requireiot/MySoilSensorESP32/hardware/MySoilSensorESP32.kicad_sch

## KiCad design hardware/MySoilSensorESP32.kicad_sch (2024-08-03, an earlier design)

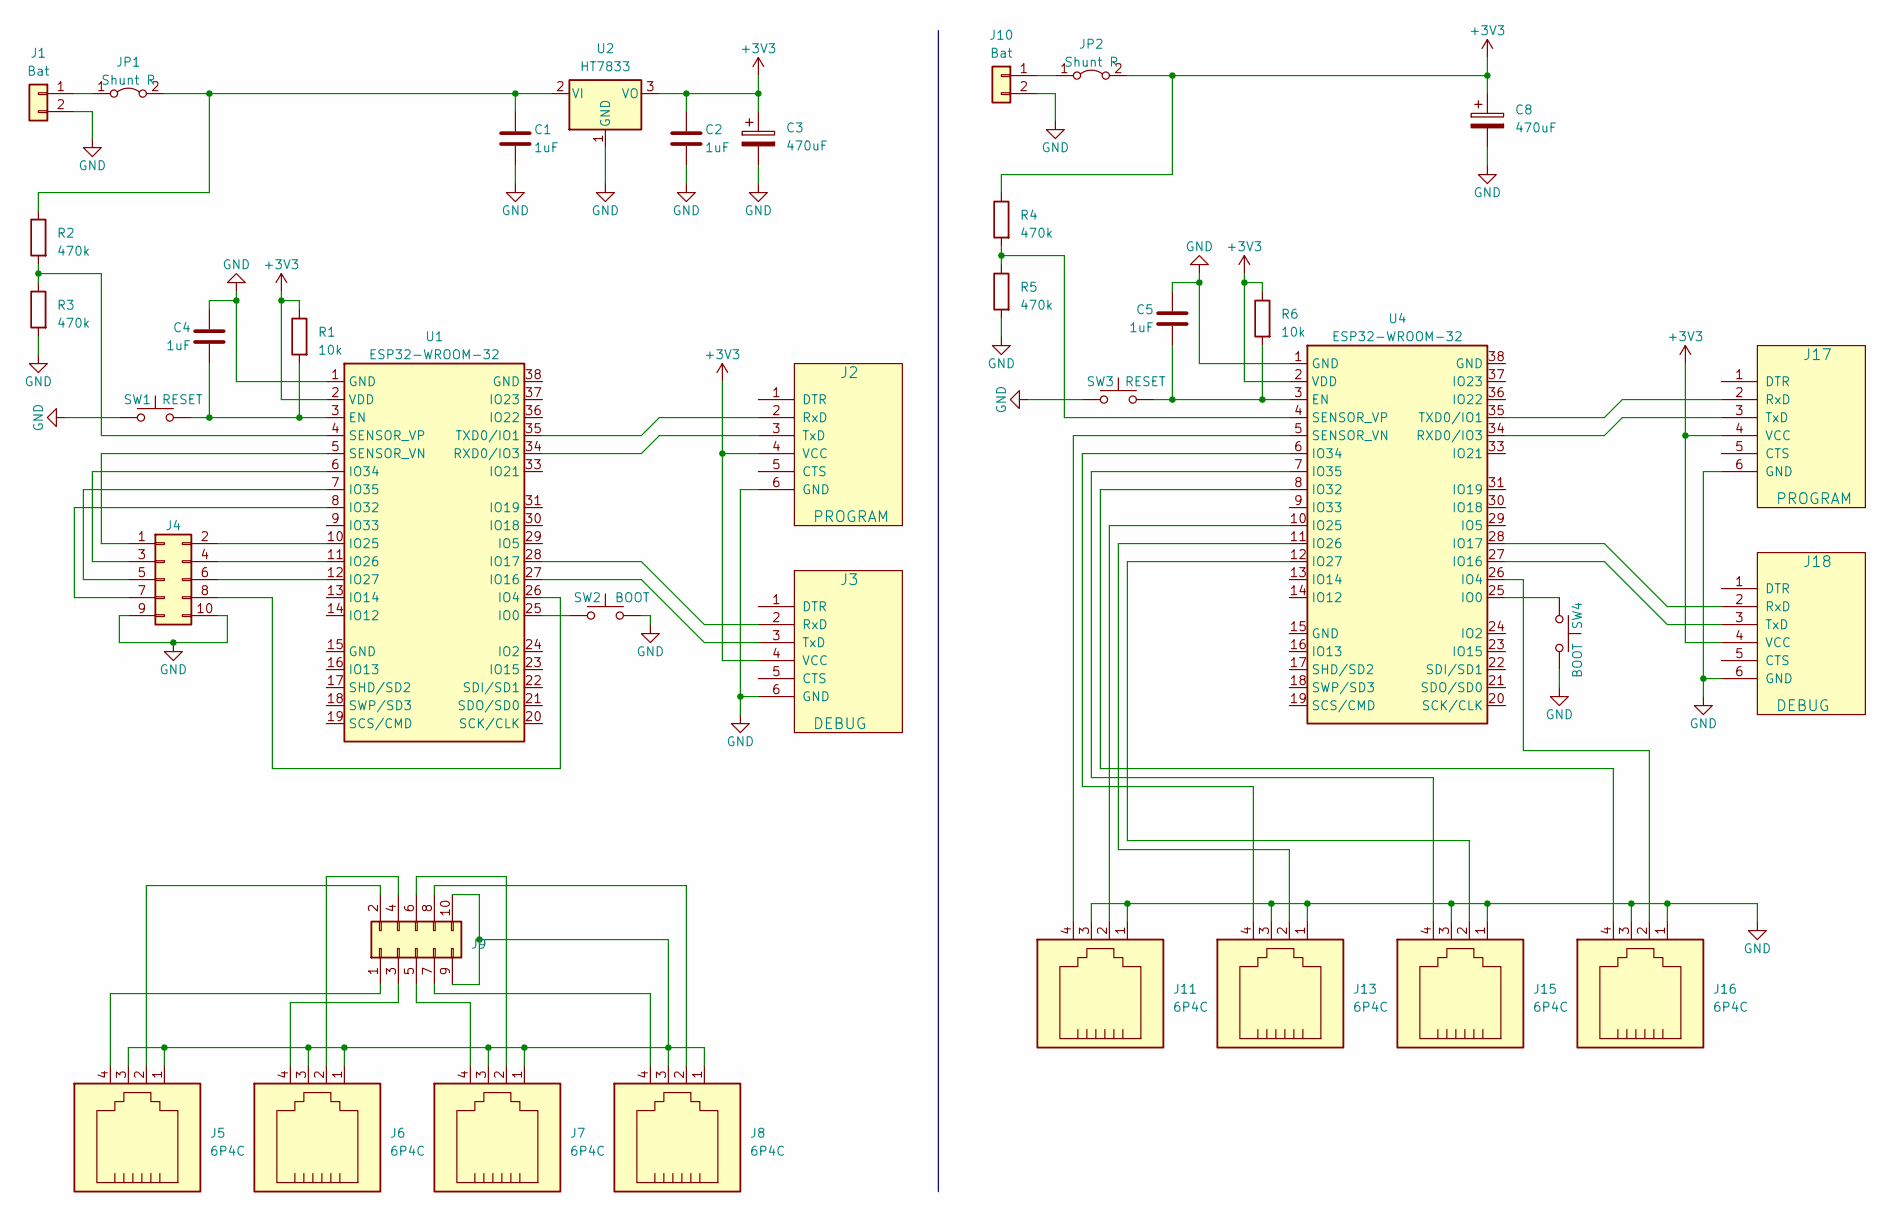
[picture p10: schematic MySoilSensorESP32.kicad_sch]

Parts:
C1, C2, C4, C5: 1uF
C3, C8: 470uF
J1, J10: Bat
J2, J17: PROGRAM
J3, J18: DEBUG
J4, J9: (no value)
J5, J6, J7, J11, J13, J15: 6P4C
J8, J16: 6P4C; RJ12_Amphenol_54601
JP1, JP2: Shunt R
R1, R6: 10k
R2, R3, R4, R5: 470k
SW1, SW3: RESET
SW2, SW4: BOOT
U1, U4: ESP32-WROOM-32
U2: HT7833; TO-92_Inline

Connections:
+3V3: C2.1, C3.1, C8.1, J2.4 (VCC), J3.4 (VCC), J17.4 (VCC), J18.4 (VCC), JP2.2 (B), R1.1, R4.1, R6.1, U1.2 (VDD), U2.3 (VO), U4.2 (VDD)
GND: C1.2, C2.2, C3.2, C4.1, C5.1, C8.2, J1.2, J2.6 (GND), J3.6 (GND), J4.9, J4.10, J10.2, J11.1, J11.3, J13.1, J13.3, J15.1, J15.3, J16.1, J16.3, J17.6 (GND), J18.6 (GND), R3.2, R5.2, SW1.1, SW2.2, SW3.1, SW4.2, U1.1 (GND), U2.1 (GND), U4.1 (GND)
unnamed: C1.1, JP1.2 (B), R2.1, U2.2 (VI)
unnamed: C4.2, R1.2, SW1.2, U1.3 (EN)
unnamed: C5.2, R6.2, SW3.2, U4.3 (EN)
unnamed: J1.1, JP1.1 (A)
unnamed: J2.2 (RxD), U1.35 (TXD0/IO1)
unnamed: J2.3 (TxD), U1.34 (RXD0/IO3)
unnamed: J3.2 (RxD), U1.28 (IO17)
unnamed: J3.3 (TxD), U1.27 (IO16)
unnamed: J4.1, U1.5 (SENSOR_VN)
unnamed: J4.2, U1.10 (IO25)
unnamed: J4.3, U1.6 (IO34)
unnamed: J4.4, U1.11 (IO26)
unnamed: J4.5, U1.7 (IO35)
unnamed: J4.6, U1.12 (IO27)
unnamed: J4.7, U1.8 (IO32)
unnamed: J4.8, U1.26 (IO4)
unnamed: J5.1, J5.3, J6.1, J6.3, J7.1, J7.3, J8.1, J8.3, J9.9, J9.10
unnamed: J5.2, J9.2
unnamed: J5.4, J9.1
unnamed: J6.2, J9.4
unnamed: J6.4, J9.3
unnamed: J7.2, J9.6
unnamed: J7.4, J9.5
unnamed: J8.2, J9.8
unnamed: J8.4, J9.7
unnamed: J10.1, JP2.1 (A)
unnamed: J11.2, U4.10 (IO25)
unnamed: J11.4, U4.5 (SENSOR_VN)
unnamed: J13.2, U4.11 (IO26)
unnamed: J13.4, U4.6 (IO34)
unnamed: J15.2, U4.12 (IO27)
unnamed: J15.4, U4.7 (IO35)
unnamed: J16.2, U4.26 (IO4)
unnamed: J16.4, U4.8 (IO32)
unnamed: J17.2 (RxD), U4.35 (TXD0/IO1)
unnamed: J17.3 (TxD), U4.34 (RXD0/IO3)
unnamed: J18.2 (RxD), U4.28 (IO17)
unnamed: J18.3 (TxD), U4.27 (IO16)
unnamed: R2.2, R3.1, U1.4 (SENSOR_VP)
unnamed: R4.2, R5.1, U4.4 (SENSOR_VP)
unnamed: SW2.1, U1.25 (IO0)
unnamed: SW4.1, U4.25 (IO0)
