requireiot/MySoilSensorESP32/src/myauth_sample.h

#ifndef __MYAUTH_H
#define __MYAUTH_H

// fill in your real Wifi information and save as "myauth.h"

#define WIFI_SSID       "my-wifi-ssid"
#define WIFI_PASSWORD   "my-secret-wifi-password"

//#define QUICK // shortened timing, for debugging only

#endif // __MYAUTH_H
